tsuyoshiohashi/SDR_Transmitter_for_Raspi/hat/all_mode_tx_3.kicad_sch

## KiCad design hat/all_mode_tx_3.kicad_sch (2022-12-20)

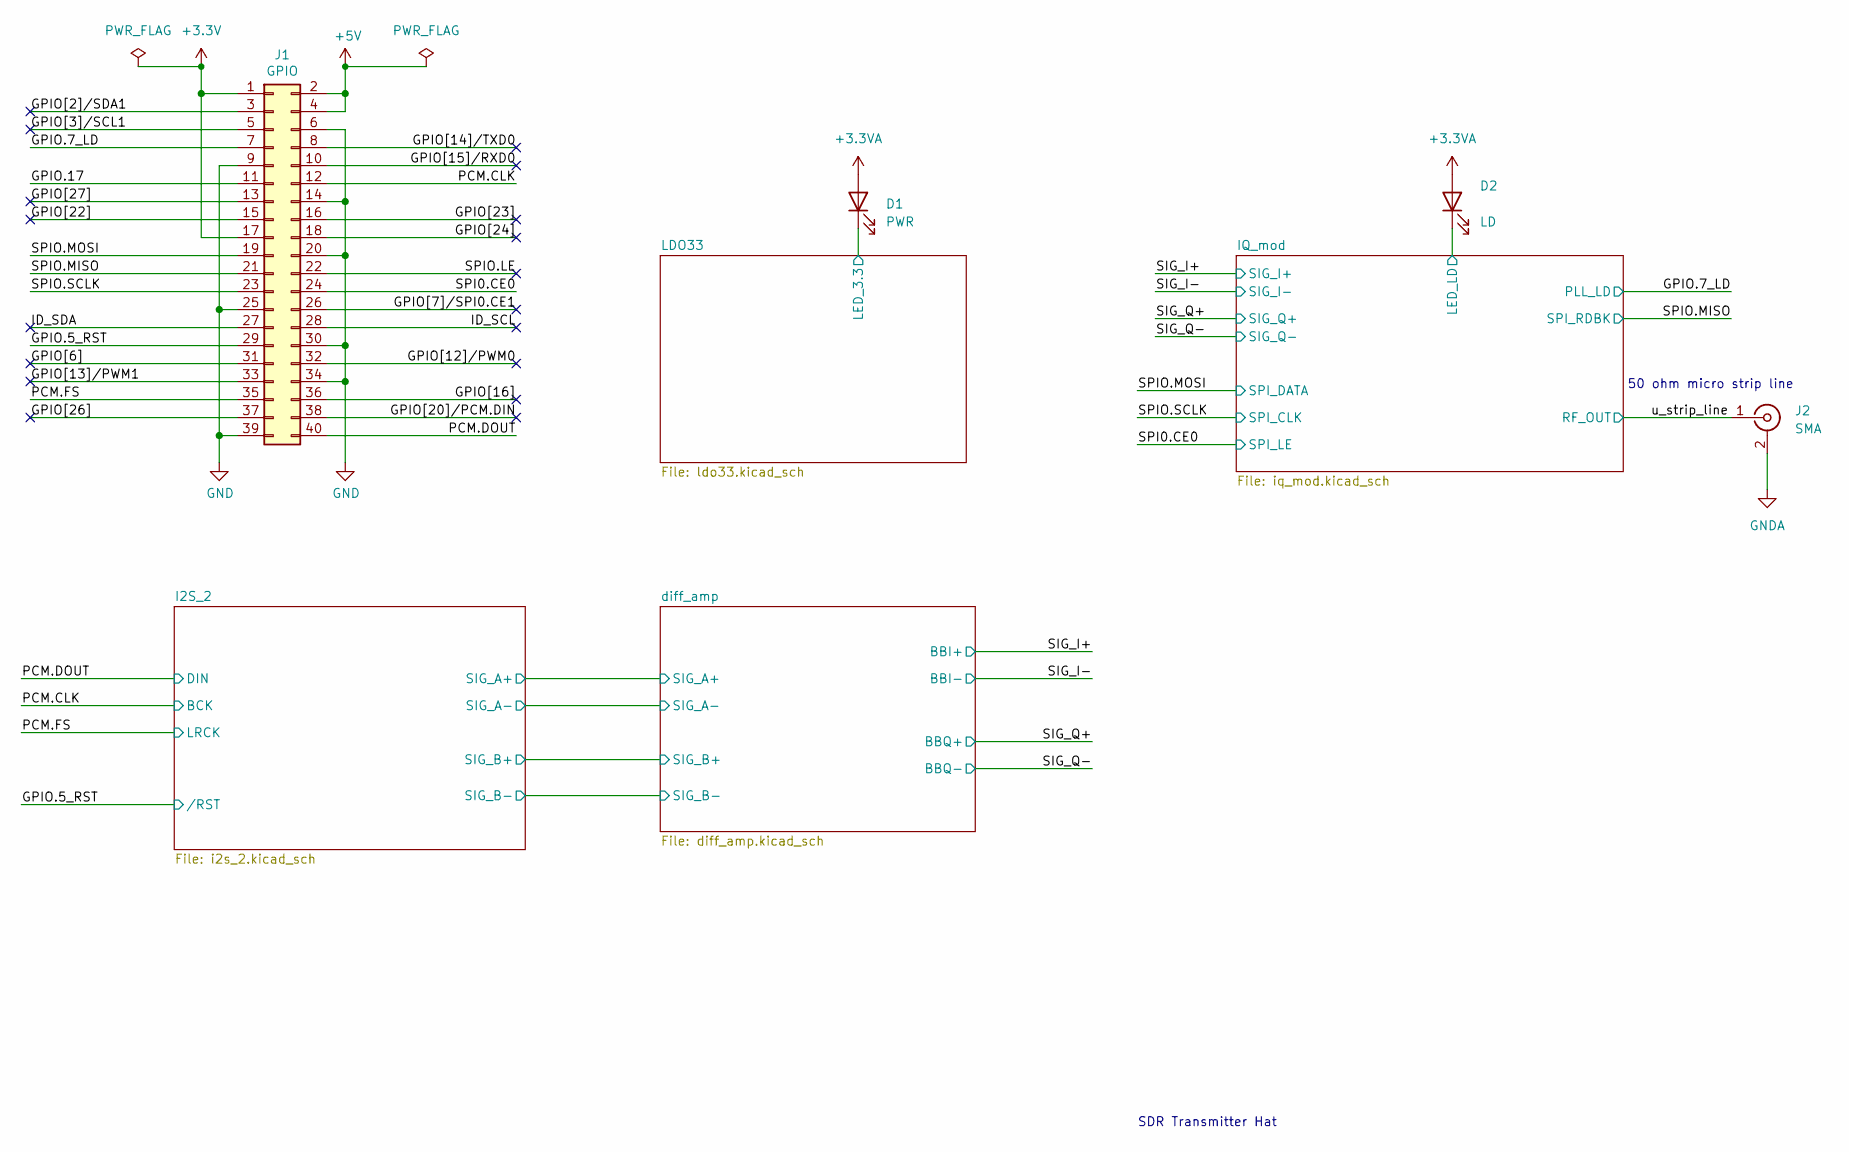
[picture p9: schematic all_mode_tx_3.kicad_sch]

Parts:
D1: PWR; LED_0603_1608Metric_Pad1.05x0.95mm_HandSolder
D2: LD; LED_0603_1608Metric_Pad1.05x0.95mm_HandSolder
J1: GPIO; PinSocket_2x20_P2.54mm_Vertical
J2: SMA; SMA_Molex_73251-1153_EdgeMount_Horizontal

Connections:
+3.3V: J1.1, J1.17
+3.3VA: D1.2 (A), D2.2 (A)
+5V: J1.2, J1.4
GND: J1.6, J1.9, J1.14, J1.20, J1.25, J1.30, J1.34, J1.39
GNDA: J2.2 (Ext)
GPIO.5_RST: J1.29
GPIO.7_LD: J1.7
GPIO.17: J1.11
GPIO[2]/SDA1: J1.3
GPIO[3]/SCL1: J1.5
GPIO[6]: J1.31
GPIO[7]/SPI0.CE1: J1.26
GPIO[12]/PWM0: J1.32
GPIO[13]/PWM1: J1.33
GPIO[14]/TXD0: J1.8
GPIO[15]/RXD0: J1.10
GPIO[16]: J1.36
GPIO[20]/PCM.DIN: J1.38
GPIO[22]: J1.15
GPIO[23]: J1.16
GPIO[24]: J1.18
GPIO[26]: J1.37
GPIO[27]: J1.13
ID_SCL: J1.28
ID_SDA: J1.27
LED_3.3: D1.1 (K)
LED_LD: D2.1 (K)
PCM.CLK: J1.12
PCM.DOUT: J1.40
PCM.FS: J1.35
SPI0.CE0: J1.24
SPIO.LE: J1.22
SPIO.MISO: J1.21
SPIO.MOSI: J1.19
SPIO.SCLK: J1.23
u_strip_line: J2.1 (In)

Notes on the sheet:
50 ohm micro strip line
SDR Transmitter Hat
