tsuyoshiohashi/SDR_Transmitter_for_Raspi/hat/diff_amp.kicad_sch

## KiCad design hat/diff_amp.kicad_sch (2022-12-20)

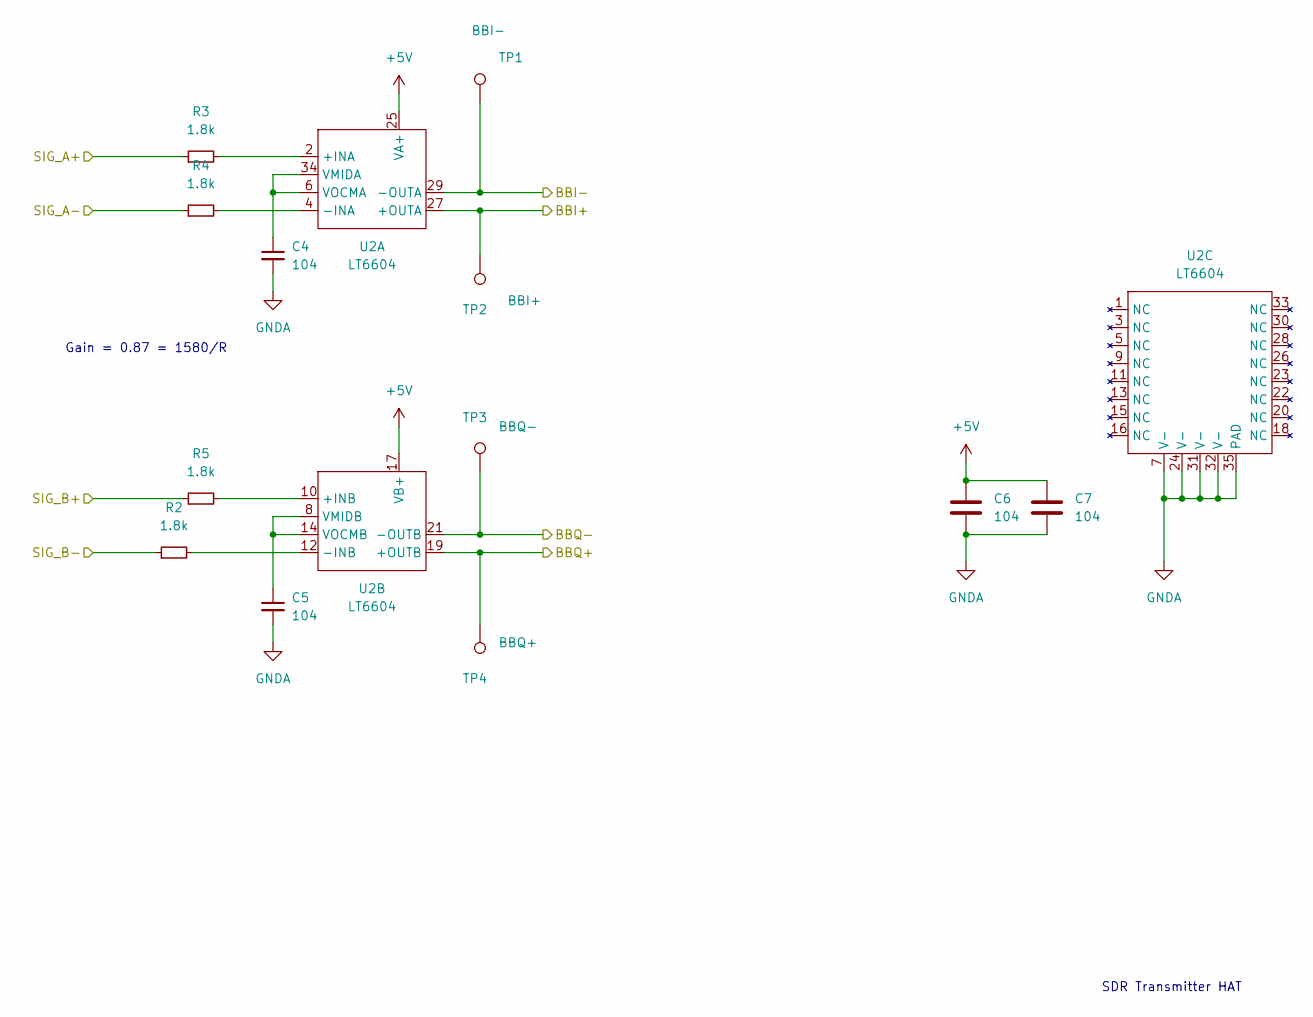
[picture p10: schematic diff_amp.kicad_sch]

Parts:
C4, C5, C6, C7: 104; C_0603_1608Metric_Pad1.08x0.95mm_HandSolder
R2, R3, R4, R5: 1.8k; R_0603_1608Metric_Pad0.98x0.95mm_HandSolder
TP1: BBI-; TestPoint_Pad_D2.0mm
TP2: BBI+; TestPoint_Pad_D2.0mm
TP3: BBQ-; TestPoint_Pad_D2.0mm
TP4: BBQ+; TestPoint_Pad_D2.0mm
U2: LT6604; LT6604IUFF-2.5-PBF

Connections:
+5V: C6.1, C7.1, U2.17 (VB+), U2.25 (VA+)
BBI+: TP2.1, U2.27 (+OUTA)
BBI-: TP1.1, U2.29 (-OUTA)
BBQ+: TP4.1, U2.19 (+OUTB)
BBQ-: TP3.1, U2.21 (-OUTB)
GNDA: C4.2, C5.2, C6.2, C7.2, U2.7 (V-), U2.24 (V-), U2.31 (V-), U2.32 (V-), U2.35 (PAD)
unnamed: C4.1, U2.6 (VOCMA), U2.34 (VMIDA)
unnamed: C5.1, U2.8 (VMIDB), U2.14 (VOCMB)
unnamed: R2.2, U2.12 (-INB)
unnamed: R3.2, U2.2 (+INA)
unnamed: R4.2, U2.4 (-INA)
unnamed: R5.2, U2.10 (+INB)
SIG_A+: R3.1
SIG_A-: R4.1
SIG_B+: R5.1
SIG_B-: R2.1

Notes on the sheet:
Gain = 0.87 = 1580/R
SDR Transmitter HAT
