tsuyoshiohashi/SDR_Transmitter_for_Raspi/hat/i2s_2.kicad_sch

## KiCad design hat/i2s_2.kicad_sch (2022-12-20)

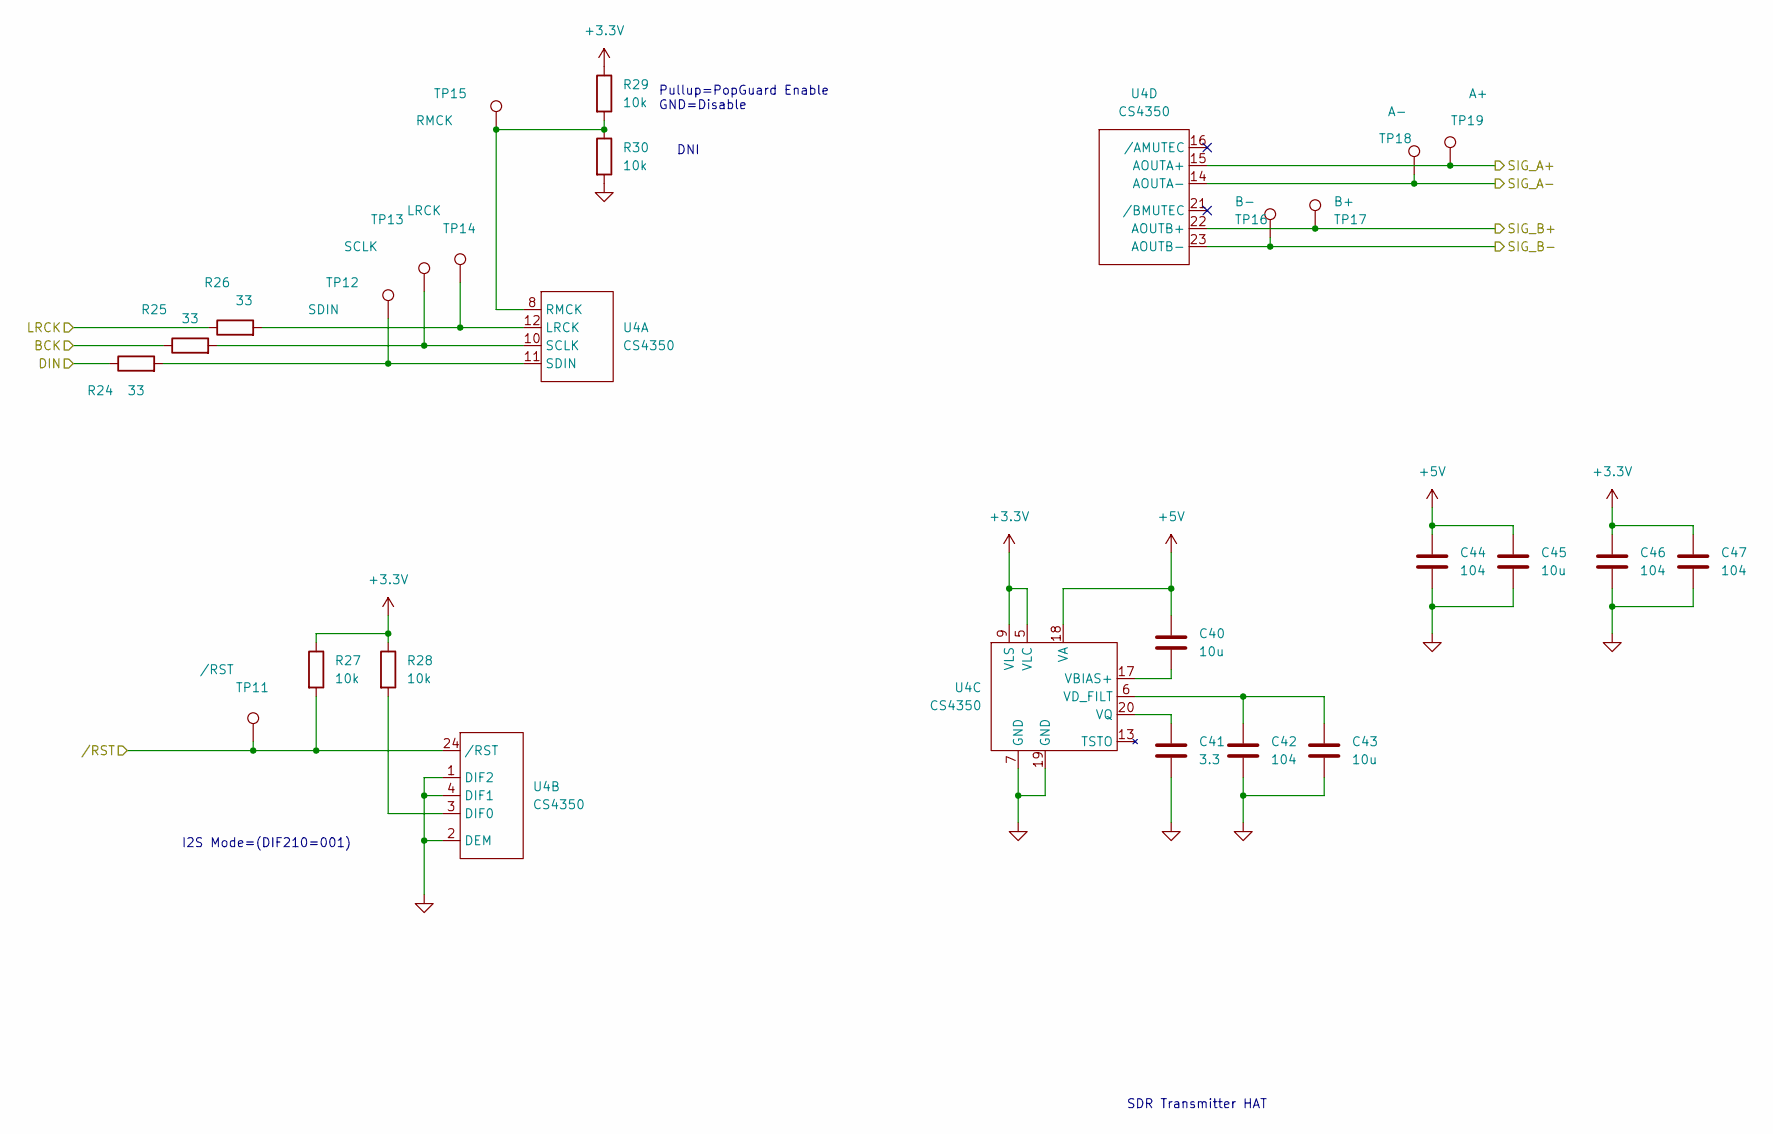
[picture p11: schematic i2s_2.kicad_sch]

Parts:
C40, C43, C45: 10u; C_0603_1608Metric_Pad1.08x0.95mm_HandSolder
C41: 3.3; C_0603_1608Metric_Pad1.08x0.95mm_HandSolder
C42, C44, C46, C47: 104; C_0603_1608Metric_Pad1.08x0.95mm_HandSolder
R24, R25, R26: 33; R_0603_1608Metric_Pad0.98x0.95mm_HandSolder
R27, R28, R29, R30: 10k; R_0603_1608Metric_Pad0.98x0.95mm_HandSolder
TP11: /RST; TestPoint_Pad_D2.0mm
TP12: SDIN; TestPoint_Pad_D2.0mm
TP13: SCLK; TestPoint_Pad_D2.0mm
TP14: LRCK; TestPoint_Pad_D2.0mm
TP15: RMCK; TestPoint_Pad_D2.0mm
TP16: B-; TestPoint_Pad_D2.0mm
TP17: B+; TestPoint_Pad_D2.0mm
TP18: A-; TestPoint_Pad_D2.0mm
TP19: A+; TestPoint_Pad_D2.0mm
U4: CS4350; TSSOP-24_4.4x7.8mm_P0.65mm

Connections:
+3.3V: C46.1, C47.1, R27.1, R28.1, R29.1, U4.5 (VLC), U4.9 (VLS)
+5V: C40.1, C44.1, C45.1, U4.18 (VA)
BCK: R25.1
DIN: R24.1
LRCK: R26.1
unnamed: C40.2, U4.17 (VBIAS+)
unnamed: C41.1, U4.20 (VQ)
unnamed: C42.1, C43.1, U4.6 (VD_FILT)
unnamed: R24.2, TP12.1, U4.11 (SDIN)
unnamed: R25.2, TP13.1, U4.10 (SCLK)
unnamed: R26.2, TP14.1, U4.12 (LRCK)
unnamed: R28.2, U4.3 (DIF0)
unnamed: R29.2, R30.1, TP15.1, U4.8 (RMCK)
SIG_A+: TP19.1, U4.15 (AOUTA+)
SIG_A-: TP18.1, U4.14 (AOUTA-)
SIG_B+: TP17.1, U4.22 (AOUTB+)
SIG_B-: TP16.1, U4.23 (AOUTB-)
/RST: R27.2, TP11.1, U4.24 (/RST)
~: C41.2, C42.2, C43.2, C44.2, C45.2, C46.2, C47.2, R30.2, U4.1 (DIF2), U4.2 (DEM), U4.4 (DIF1), U4.7 (GND), U4.19 (GND)

Notes on the sheet:
I2S Mode=(DIF210=001)
Pullup=PopGuard Enable GND=Disable
DNI
SDR Transmitter HAT
