tsuyoshiohashi/SDR_Transmitter_for_Raspi/hat/iq_mod.kicad_sch

## KiCad design hat/iq_mod.kicad_sch (2022-12-20)

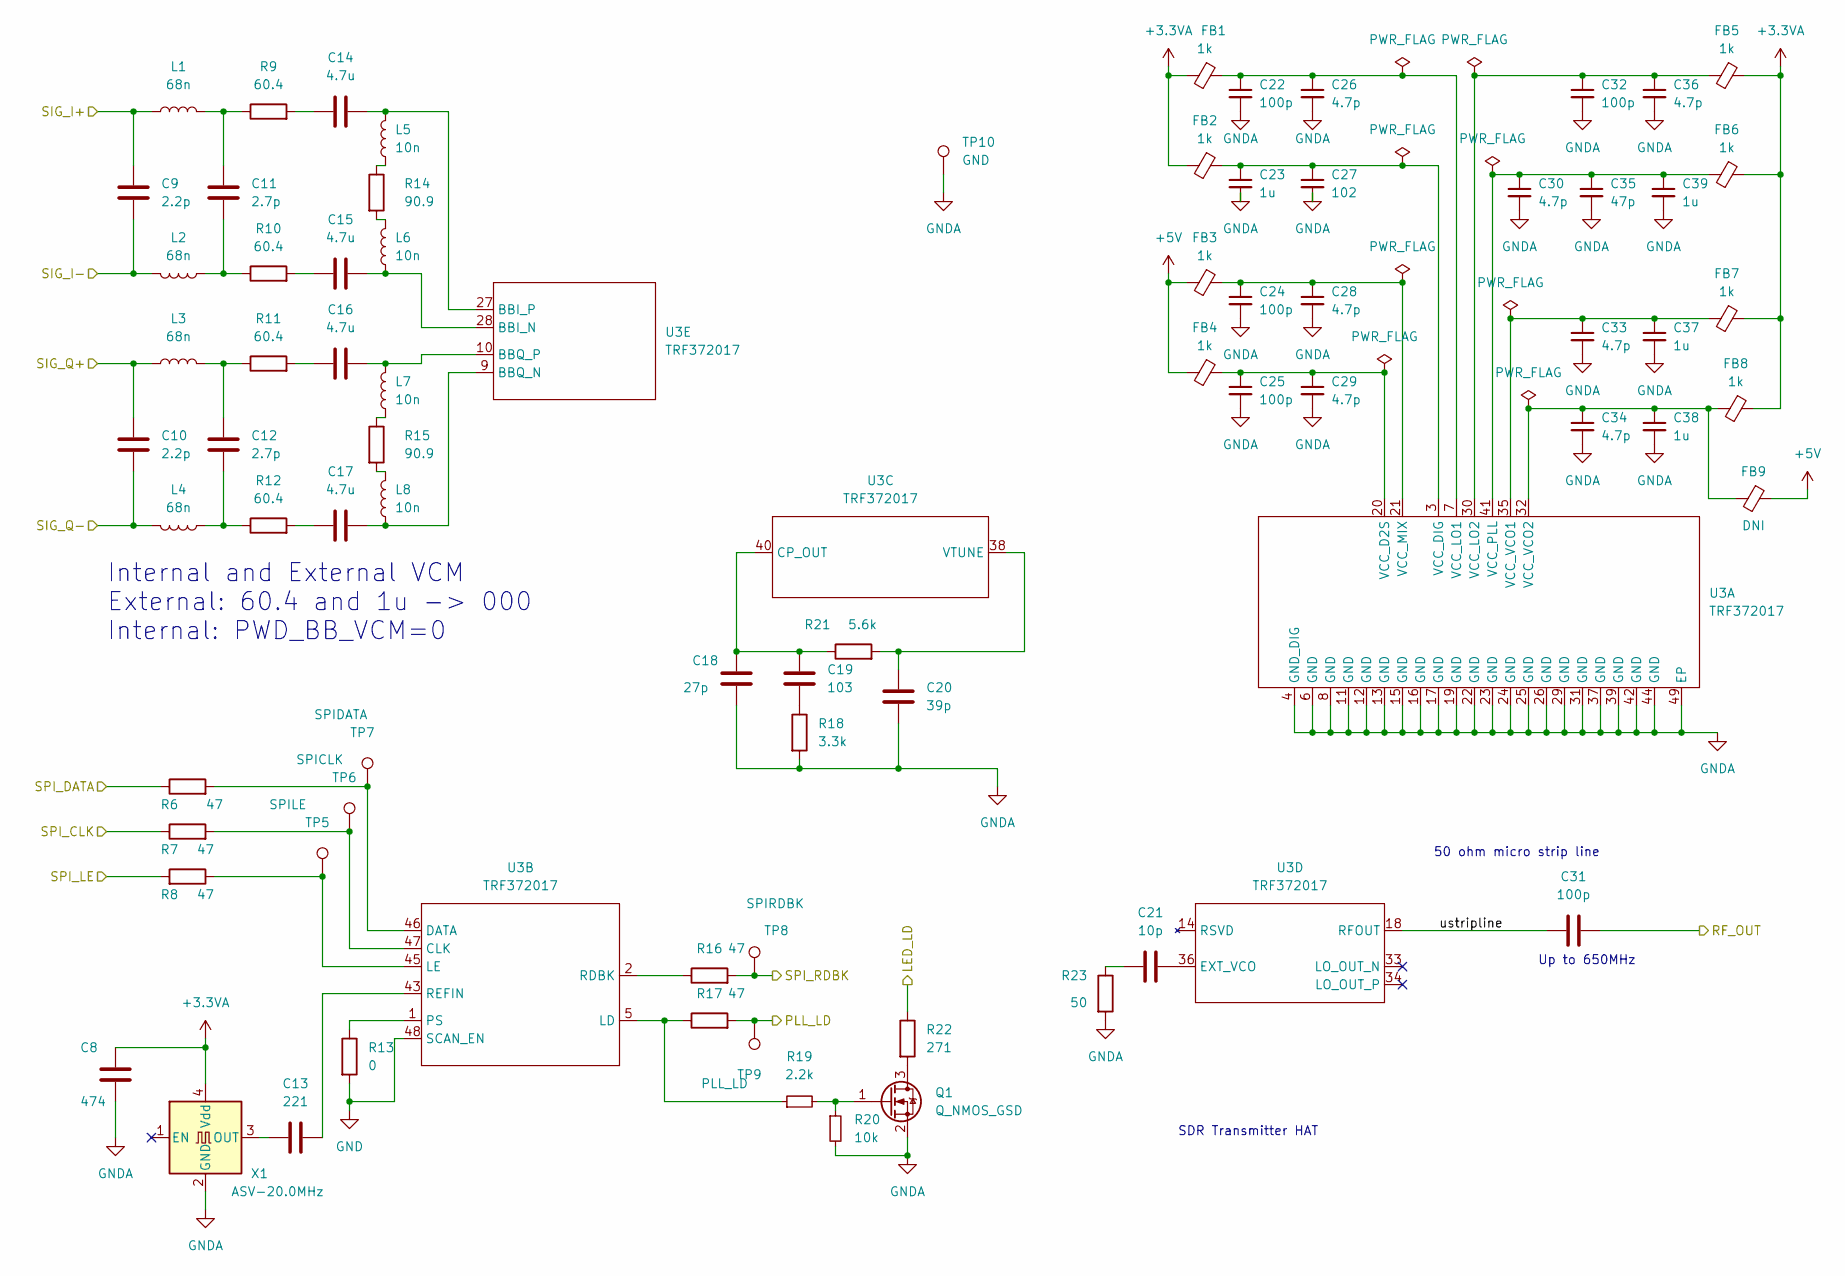
[picture p12: schematic iq_mod.kicad_sch]

Parts:
C8: 474; C_0603_1608Metric_Pad1.08x0.95mm_HandSolder
C9, C10: 2.2p; C_0603_1608Metric_Pad1.08x0.95mm_HandSolder
C11, C12: 2.7p; C_0603_1608Metric_Pad1.08x0.95mm_HandSolder
C13: 221; C_0603_1608Metric_Pad1.08x0.95mm_HandSolder
C14, C15, C16, C17: 4.7u; C_0603_1608Metric_Pad1.08x0.95mm_HandSolder
C18: 27p; C_0603_1608Metric_Pad1.08x0.95mm_HandSolder
C19: 103; C_0603_1608Metric_Pad1.08x0.95mm_HandSolder
C20: 39p; C_0603_1608Metric_Pad1.08x0.95mm_HandSolder
C21: 10p; C_0603_1608Metric_Pad1.08x0.95mm_HandSolder
C22, C24, C25, C31, C32: 100p; C_0603_1608Metric_Pad1.08x0.95mm_HandSolder
C23, C37, C38, C39: 1u; C_0603_1608Metric_Pad1.08x0.95mm_HandSolder
C26, C28, C29, C30, C33, C34, C36: 4.7p; C_0603_1608Metric_Pad1.08x0.95mm_HandSolder
C27: 102; C_0603_1608Metric_Pad1.08x0.95mm_HandSolder
C35: 47p; C_0603_1608Metric_Pad1.08x0.95mm_HandSolder
FB1, FB2, FB3, FB4, FB5, FB6, FB7, FB8: 1k; L_0603_1608Metric_Pad1.05x0.95mm_HandSolder
FB9: DNI; L_0603_1608Metric_Pad1.05x0.95mm_HandSolder
L1, L2, L3, L4: 68n; L_0603_1608Metric_Pad1.05x0.95mm_HandSolder
L5, L6, L7, L8: 10n; L_0603_1608Metric_Pad1.05x0.95mm_HandSolder
Q1: Q_NMOS_GSD; SOT-23
R6, R7, R8, R16, R17: 47; R_0603_1608Metric_Pad0.98x0.95mm_HandSolder
R9, R10, R11, R12: 60.4; R_0603_1608Metric_Pad0.98x0.95mm_HandSolder
R13: 0; R_0603_1608Metric_Pad0.98x0.95mm_HandSolder
R14, R15: 90.9; R_0603_1608Metric_Pad0.98x0.95mm_HandSolder
R18: 3.3k; R_0603_1608Metric_Pad0.98x0.95mm_HandSolder
R19: 2.2k; R_0603_1608Metric_Pad0.98x0.95mm_HandSolder
R20: 10k; R_0603_1608Metric_Pad0.98x0.95mm_HandSolder
R21: 5.6k; R_0603_1608Metric_Pad0.98x0.95mm_HandSolder
R22: 271; R_0603_1608Metric_Pad0.98x0.95mm_HandSolder
R23: 50; R_0603_1608Metric_Pad0.98x0.95mm_HandSolder
TP5: SPILE; TestPoint_Pad_D2.0mm
TP6: SPICLK; TestPoint_Pad_D2.0mm
TP7: SPIDATA; TestPoint_Pad_D2.0mm
TP8: SPIRDBK; TestPoint_Pad_D2.0mm
TP9: PLL_LD; TestPoint_Pad_D2.0mm
TP10: GND; TestPoint_Pad_D2.5mm
U3: TRF372017; VQFN-48-1EP_7x7mm_P0.5mm_EP5.15x5.15mm_ThermalVias
X1: ASV-20.0MHz; Oscillator_SMD_Abracon_ASV-4Pin_7.0x5.1mm

Connections:
+3.3VA: C8.1, FB1.2, FB2.2, FB5.1, FB6.1, FB7.1, FB8.1, X1.4 (Vdd)
+5V: FB3.2, FB4.2, FB9.1
GND: R13.2, U3.48 (SCAN_EN)
GNDA: C8.2, C18.2, C20.2, C22.2, C23.2, C24.2, C25.2, C26.2, C27.2, C28.2, C29.2, C30.2, C32.2, C33.2, C34.2, C35.2, C36.2, C37.2, C38.2, C39.2, Q1.2 (S), R18.2, R20.2, R23.2, TP10.1, U3.4 (GND_DIG), U3.6 (GND), U3.8 (GND), U3.11 (GND), U3.12 (GND), U3.13 (GND), U3.15 (GND), U3.16 (GND), U3.17 (GND), U3.19 (GND), U3.22 (GND), U3.23 (GND), U3.24 (GND), U3.25 (GND), U3.26 (GND), U3.29 (GND), U3.31 (GND), U3.37 (GND), U3.39 (GND), U3.42 (GND), U3.44 (GND), U3.49 (EP), X1.2 (GND)
LED_LD: R22.1
unnamed: C11.1, L1.2, R9.1
unnamed: C11.2, L2.2, R10.1
unnamed: C12.1, L3.2, R11.1
unnamed: C12.2, L4.2, R12.1
unnamed: C13.1, X1.3 (OUT)
unnamed: C13.2, U3.43 (REFIN)
unnamed: C14.1, R9.2
unnamed: C14.2, L5.1, U3.27 (BBI_P)
unnamed: C15.1, R10.2
unnamed: C15.2, L6.2, U3.28 (BBI_N)
unnamed: C16.1, R11.2
unnamed: C16.2, L7.1, U3.10 (BBQ_P)
unnamed: C17.1, R12.2
unnamed: C17.2, L8.2, U3.9 (BBQ_N)
unnamed: C18.1, C19.1, R21.1, U3.40 (CP_OUT)
unnamed: C19.2, R18.1
unnamed: C20.1, R21.2, U3.38 (VTUNE)
unnamed: C21.1, R23.1
unnamed: C21.2, U3.36 (EXT_VCO)
unnamed: C22.1, C26.1, FB1.1, U3.7 (VCC_LO1)
unnamed: C23.1, C27.1, FB2.1, U3.3 (VCC_DIG)
unnamed: C24.1, C28.1, FB3.1, U3.21 (VCC_MIX)
unnamed: C25.1, C29.1, FB4.1, U3.20 (VCC_D2S)
unnamed: C30.1, C35.1, C39.1, FB6.2, U3.41 (VCC_PLL)
unnamed: C32.1, C36.1, FB5.2, U3.30 (VCC_LO2)
unnamed: C33.1, C37.1, FB7.2, U3.35 (VCC_VCO1)
unnamed: C34.1, C38.1, FB8.2, FB9.2, U3.32 (VCC_VCO2)
unnamed: L5.2, R14.1
unnamed: L6.1, R14.2
unnamed: L7.2, R15.1
unnamed: L8.1, R15.2
unnamed: Q1.1 (G), R19.2, R20.1
unnamed: Q1.3 (D), R22.2
unnamed: R6.2, TP7.1, U3.46 (DATA)
unnamed: R7.2, TP6.1, U3.47 (CLK)
unnamed: R8.1, TP5.1, U3.45 (LE)
unnamed: R13.1, U3.1 (PS)
unnamed: R16.1, U3.2 (RDBK)
unnamed: R17.1, R19.1, U3.5 (LD)
PLL_LD: R17.2, TP9.1
RF_OUT: C31.2
SIG_I+: C9.1, L1.1
SIG_I-: C9.2, L2.1
SIG_Q+: C10.1, L3.1
SIG_Q-: C10.2, L4.1
SPI_CLK: R7.1
SPI_DATA: R6.1
SPI_LE: R8.2
SPI_RDBK: R16.2, TP8.1
ustripline: C31.1, U3.18 (RFOUT)

Notes on the sheet:
SDR Transmitter HAT
Up to 650MHz
50 ohm micro strip line
Internal and External VCM External: 60.4 and 1u -> 000 Internal: PWD_BB_VCM=0
