tsuyoshiohashi/SDR_Transmitter_for_Raspi/hat/ldo33.kicad_sch

## KiCad design hat/ldo33.kicad_sch (2022-12-20)

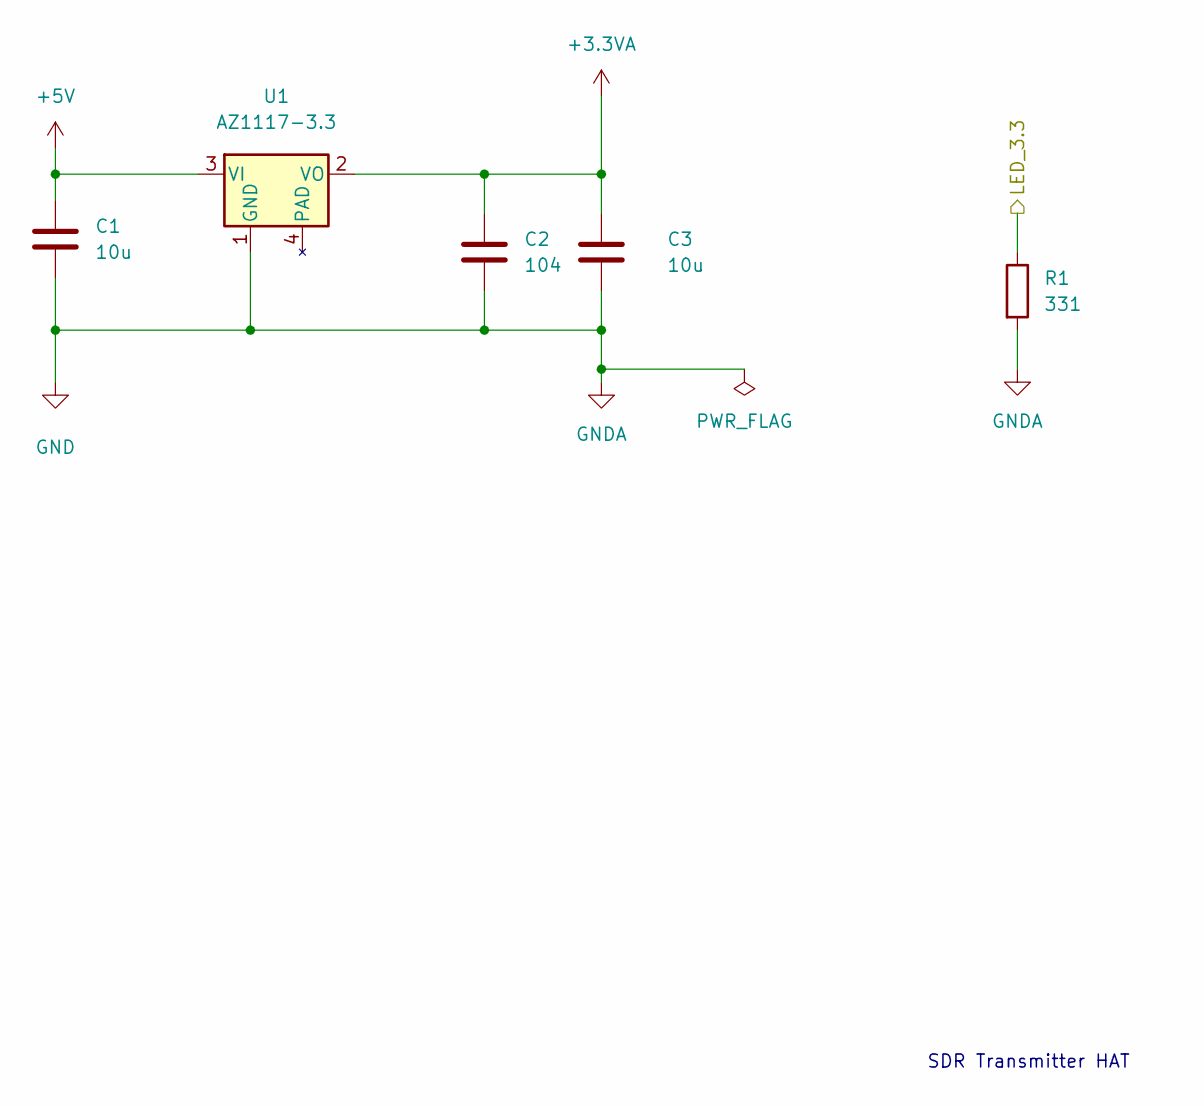
[picture p13: schematic ldo33.kicad_sch]

Parts:
C1, C3: 10u; C_0603_1608Metric_Pad1.08x0.95mm_HandSolder
C2: 104; C_0603_1608Metric_Pad1.08x0.95mm_HandSolder
R1: 331; R_0603_1608Metric_Pad0.98x0.95mm_HandSolder
U1: AZ1117-3.3; SOT-223

Connections:
+3.3VA: C2.1, C3.1, U1.2 (VO)
+5V: C1.1, U1.3 (VI)
GND: C1.2, C2.2, C3.2, R1.2, U1.1 (GND)
LED_3.3: R1.1

Notes on the sheet:
SDR Transmitter HAT
